Elecrow-RD/CrowPanel-1.46inch-HMI-ESP32-Rotary-Display/factory_soucecode/1_46_SquareLine_Studio_Project/cache/thumb_135826403oven_bj_time@3x.png

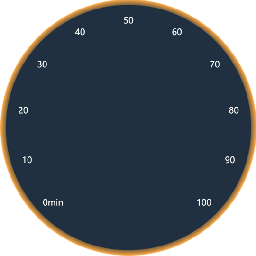
factory_soucecode/1_46_SquareLine_Studio_Project/cache/thumb_135826403oven_bj_time@3x.png
