Elecrow-RD/CrowPanel-1.46inch-HMI-ESP32-Rotary-Display/factory_soucecode/1_46_SquareLine_Studio_Project/cache/thumb_329085151bar_washing_01@3x.png

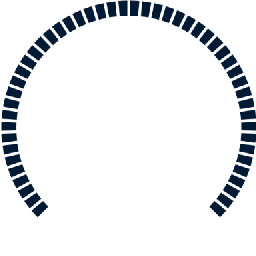
factory_soucecode/1_46_SquareLine_Studio_Project/cache/thumb_329085151bar_washing_01@3x.png
