Elecrow-RD/CrowPanel-1.46inch-HMI-ESP32-Rotary-Display/factory_soucecode/1_46_SquareLine_Studio_Project/cache/thumb_446884659椭圆 1 拷贝 2@2x.png

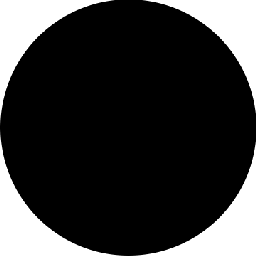
factory_soucecode/1_46_SquareLine_Studio_Project/cache/thumb_446884659椭圆 1 拷贝 2@2x.png
