Elecrow-RD/CrowPanel-1.46inch-HMI-ESP32-Rotary-Display/factory_soucecode/1_46_SquareLine_Studio_Project/cache/thumb_505009208power_on_light_mask@2x(1).png

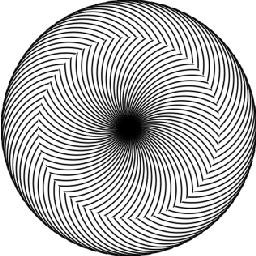
factory_soucecode/1_46_SquareLine_Studio_Project/cache/thumb_505009208power_on_light_mask@2x(1).png
