Elecrow-RD/CrowPanel-1.46inch-HMI-ESP32-Rotary-Display/factory_soucecode/1_46_SquareLine_Studio_Project/cache/thumb_869006621power_on_light_mask@3x(1).png

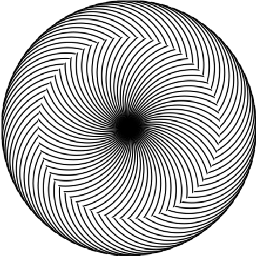
factory_soucecode/1_46_SquareLine_Studio_Project/cache/thumb_869006621power_on_light_mask@3x(1).png
