Elecrow-RD/CrowPanel-1.46inch-HMI-ESP32-Rotary-Display/factory_soucecode/1_46_SquareLine_Studio_Project/cache/thumb_950378288power_on_light_400_250707@2x.png

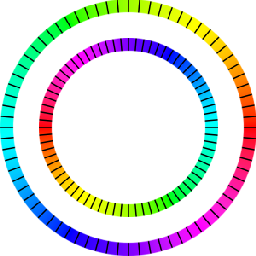
factory_soucecode/1_46_SquareLine_Studio_Project/cache/thumb_950378288power_on_light_400_250707@2x.png
