Elecrow-RD/CrowPanel-1.46inch-HMI-ESP32-Rotary-Display/factory_soucecode/1_46_SquareLine_Studio_Project/cache/thumb_1134253559light_bj_31@2x.png

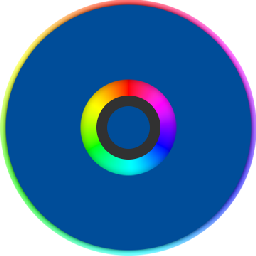
factory_soucecode/1_46_SquareLine_Studio_Project/cache/thumb_1134253559light_bj_31@2x.png
