Elecrow-RD/CrowPanel-1.46inch-HMI-ESP32-Rotary-Display/factory_soucecode/1_46_SquareLine_Studio_Project/cache/thumb_1177279941washing_bj_01@2x.png

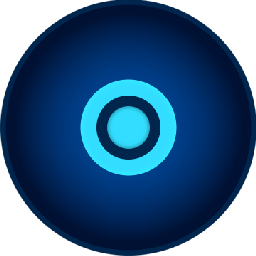
factory_soucecode/1_46_SquareLine_Studio_Project/cache/thumb_1177279941washing_bj_01@2x.png
