Elecrow-RD/CrowPanel-1.46inch-HMI-ESP32-Rotary-Display/factory_soucecode/1_46_SquareLine_Studio_Project/cache/thumb_1595359051power_on_light_280@3x.png

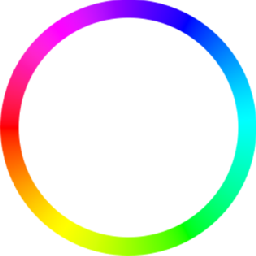
factory_soucecode/1_46_SquareLine_Studio_Project/cache/thumb_1595359051power_on_light_280@3x.png
