Elecrow-RD/CrowPanel-1.46inch-HMI-ESP32-Rotary-Display/factory_soucecode/1_46_SquareLine_Studio_Project/cache/thumb_2062386442oven_bj_01@2x.png

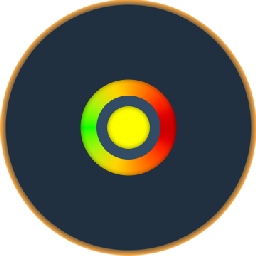
factory_soucecode/1_46_SquareLine_Studio_Project/cache/thumb_2062386442oven_bj_01@2x.png
