Elecrow-RD/CrowPanel-1.46inch-HMI-ESP32-Rotary-Display/example/V1.0/Arduino/RotaryScreen_1_46_Code_Core3_LVGL9/ui_images_build.c

#include "libraries/UI/ui_img_127450014.c"
#include "libraries/UI/ui_img_1741863219.c"
#include "libraries/UI/ui_img_1761703117.c"
#include "libraries/UI/ui_img_1854458106.c"
#include "libraries/UI/ui_img_247194651.c"
#include "libraries/UI/ui_img_32356014.c"
#include "libraries/UI/ui_img_360_1_png.c"
#include "libraries/UI/ui_img_360_bg_png.c"
#include "libraries/UI/ui_img_667923968.c"
#include "libraries/UI/ui_img_950378288.c"
#include "libraries/UI/ui_img_bar_bule_png.c"
#include "libraries/UI/ui_img_bar_orange_02_png.c"
#include "libraries/UI/ui_img_bar_white_png.c"
#include "libraries/UI/ui_img_bar_yellow_02_png.c"
#include "libraries/UI/ui_img_icon_140x400_02_png.c"
#include "libraries/UI/ui_img_screen_brightness_45_bule_png.c"
#include "libraries/UI/ui_img_screen_brightness_45_white_png.c"
